Connor-Kelly/ENGI301/docs/GUI_Diagram.png

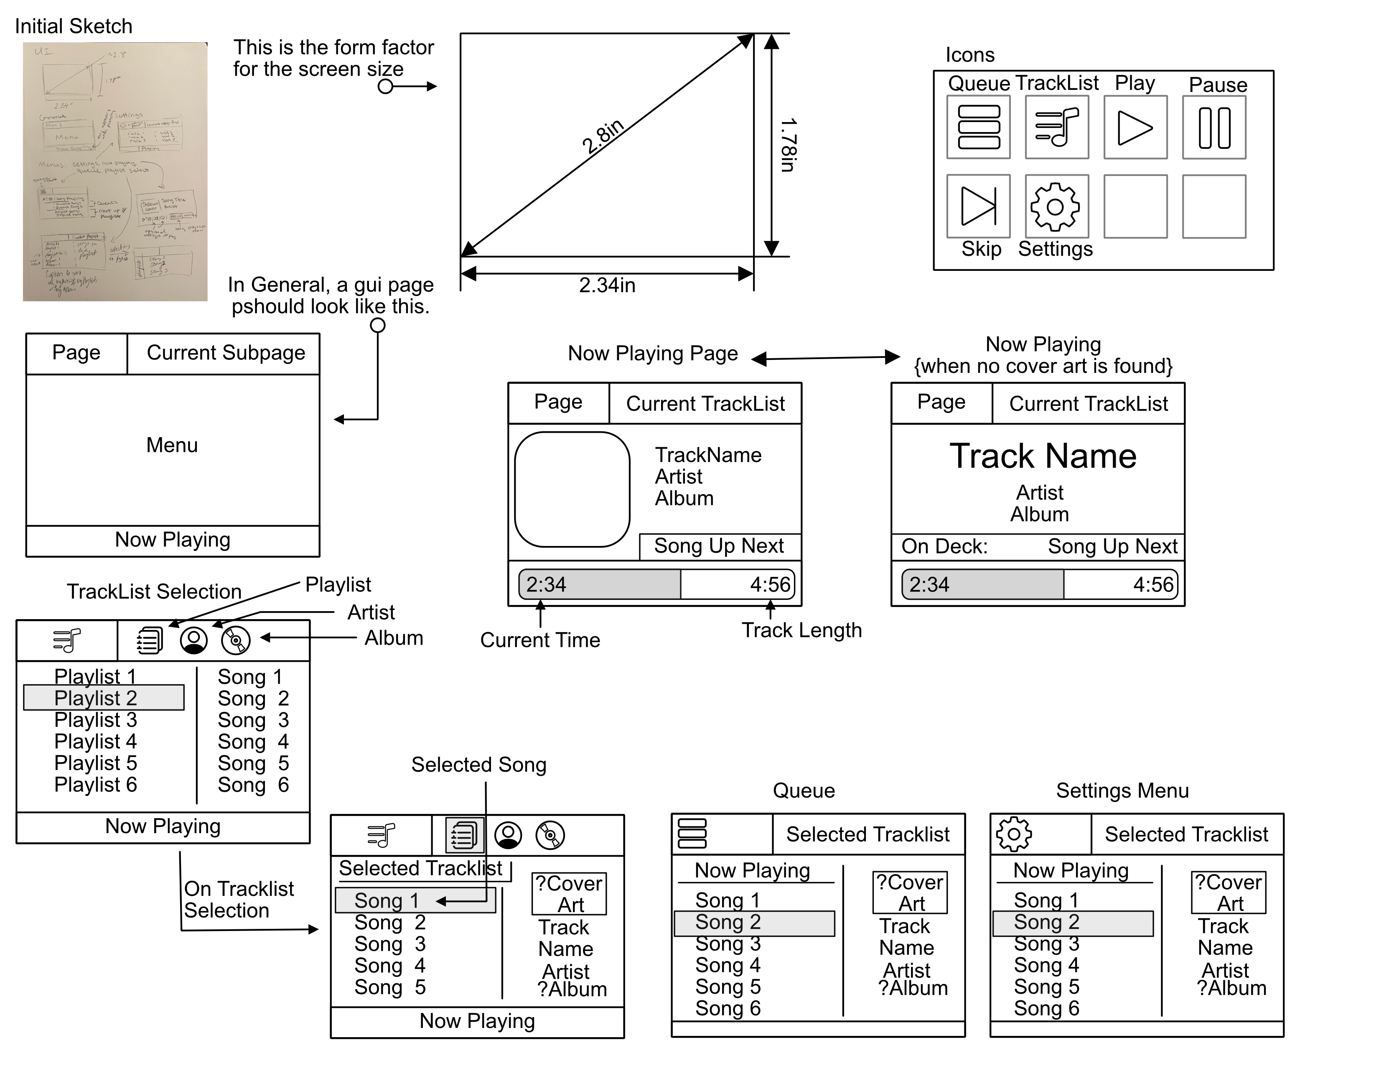
docs/GUI_Diagram.png
