Connor-Kelly/ENGI301/docs/Power_Block_Diagram.png

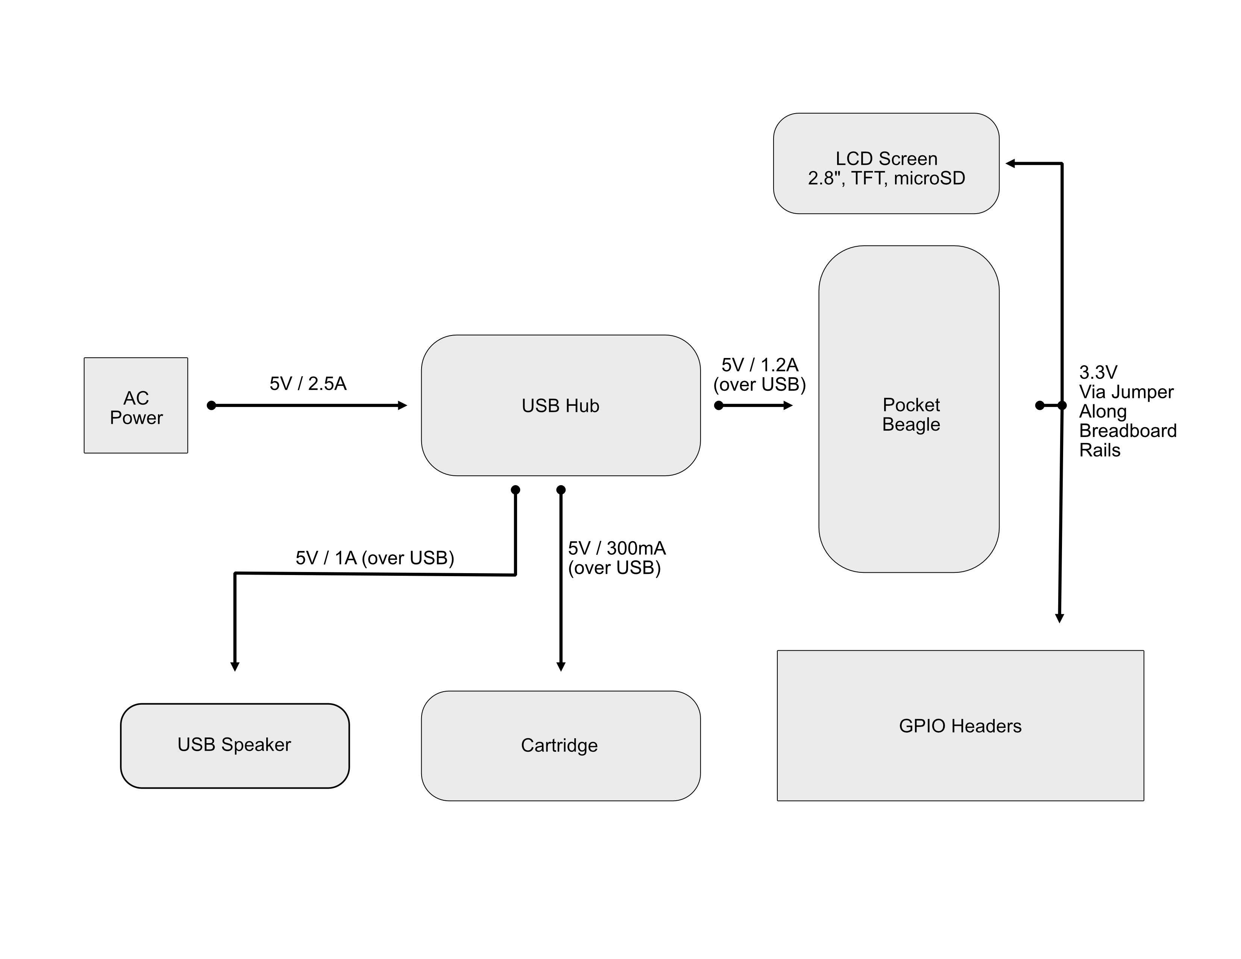
docs/Power_Block_Diagram.png
