Connor-Kelly/ENGI301/docs/Software_Diagram.png

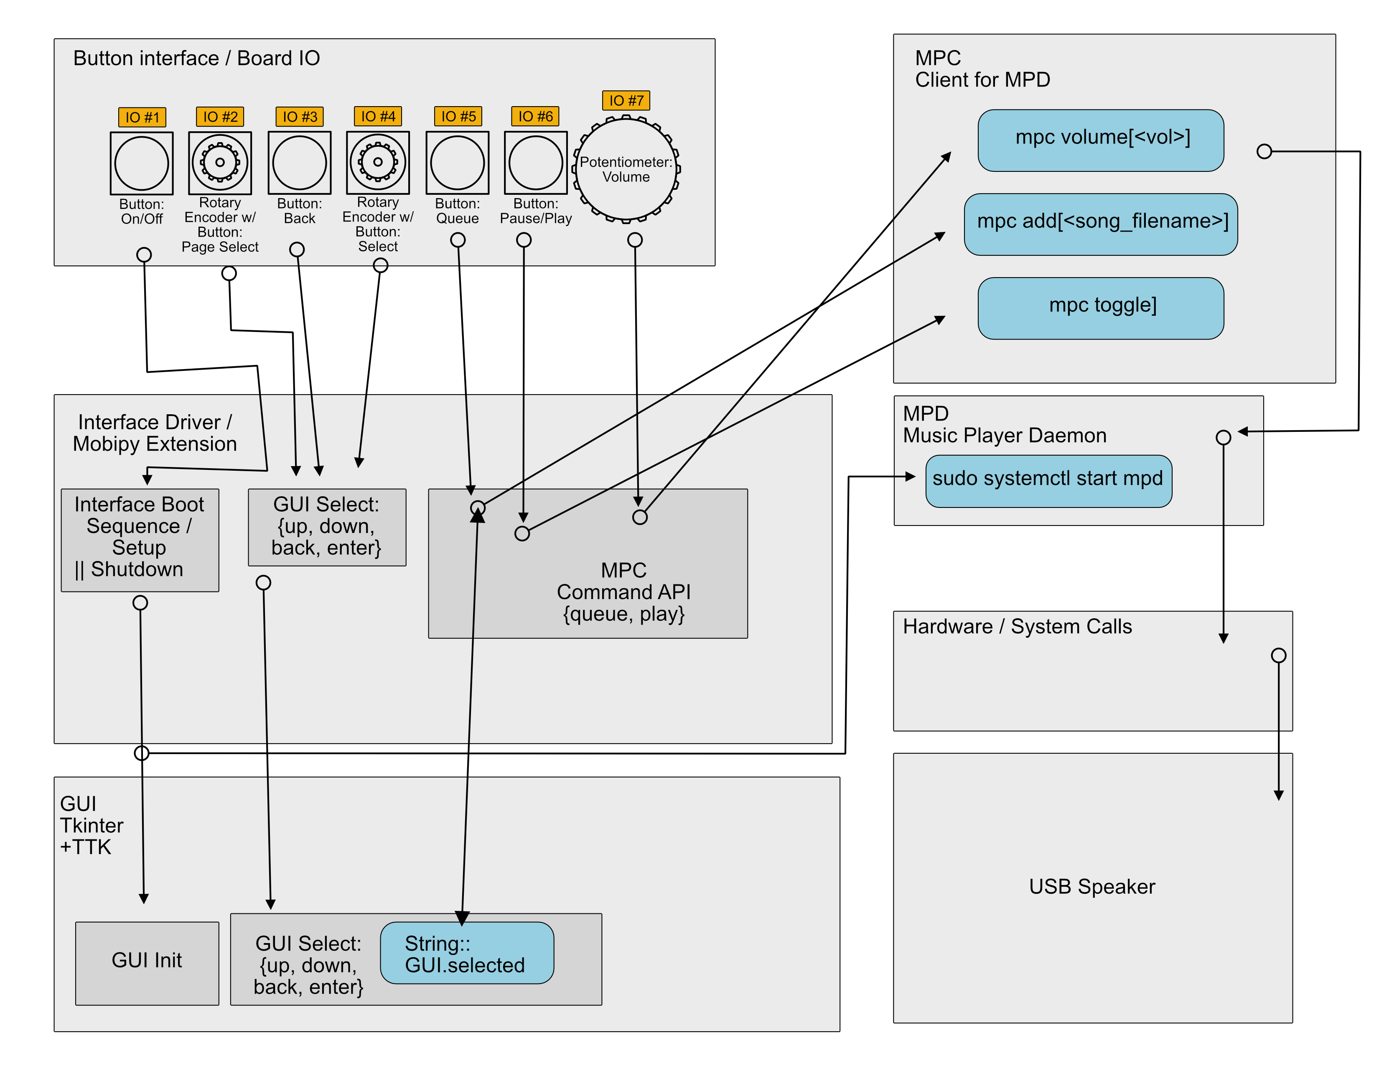
docs/Software_Diagram.png
