Connor-Kelly/ENGI301/docs/System_Block_Diagram.png

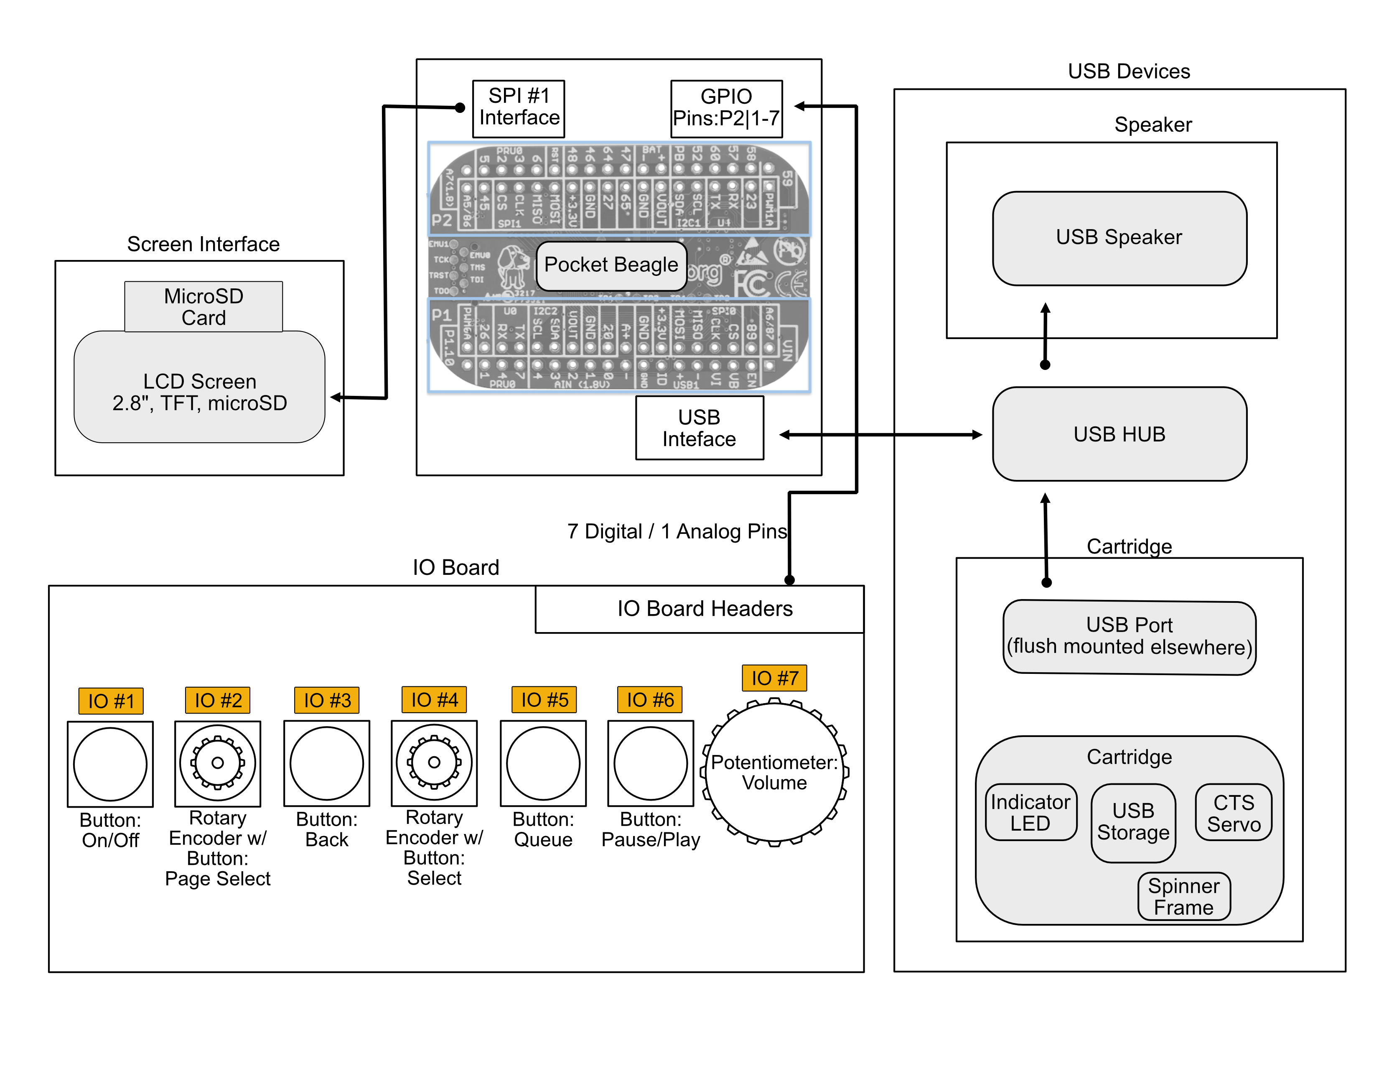
docs/System_Block_Diagram.png
