Connor-Kelly/ENGI301/project_01/images/IMG_2388.jpg

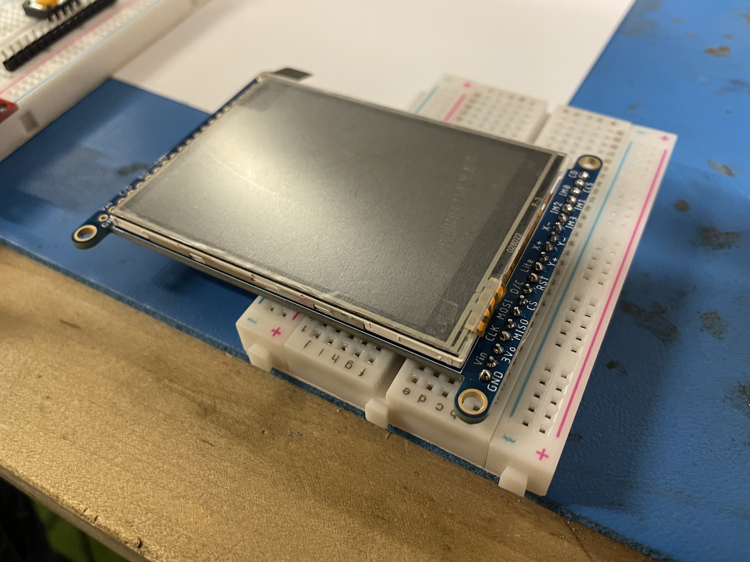
project_01/images/IMG_2388.jpg
