Connor-Kelly/ENGI301/project_01/images/IMG_2392.jpg

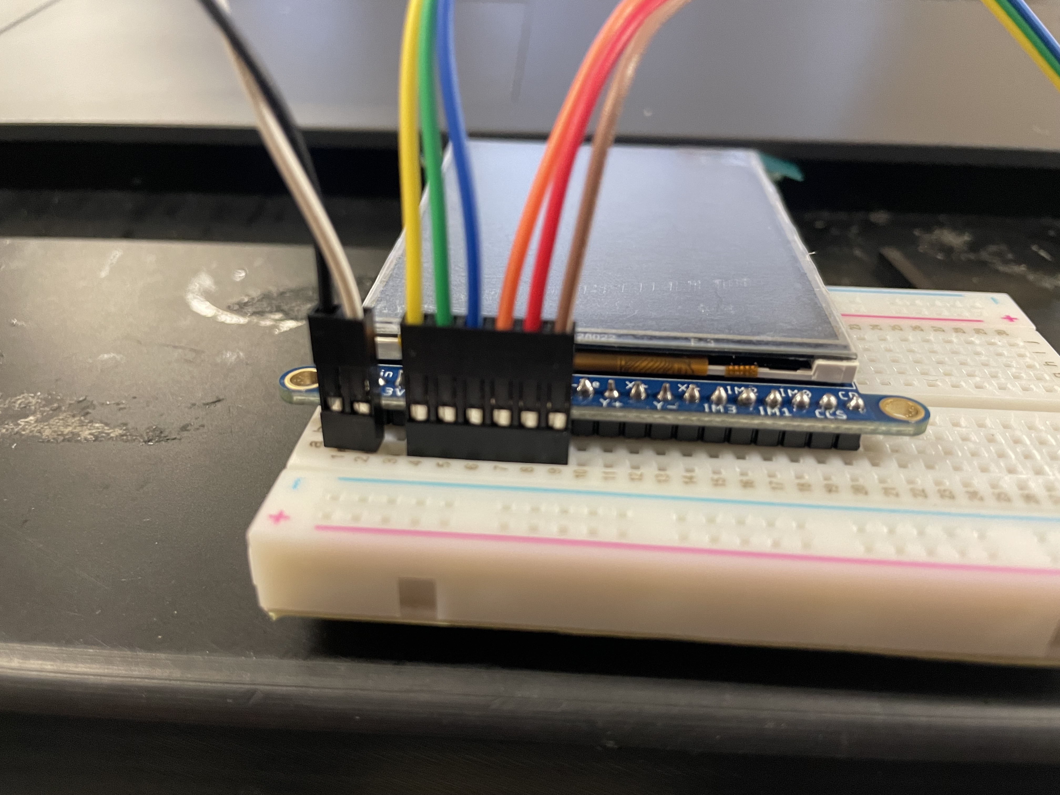
project_01/images/IMG_2392.jpg
