Connor-Kelly/ENGI301/project_01/images/IMG_2395.jpg

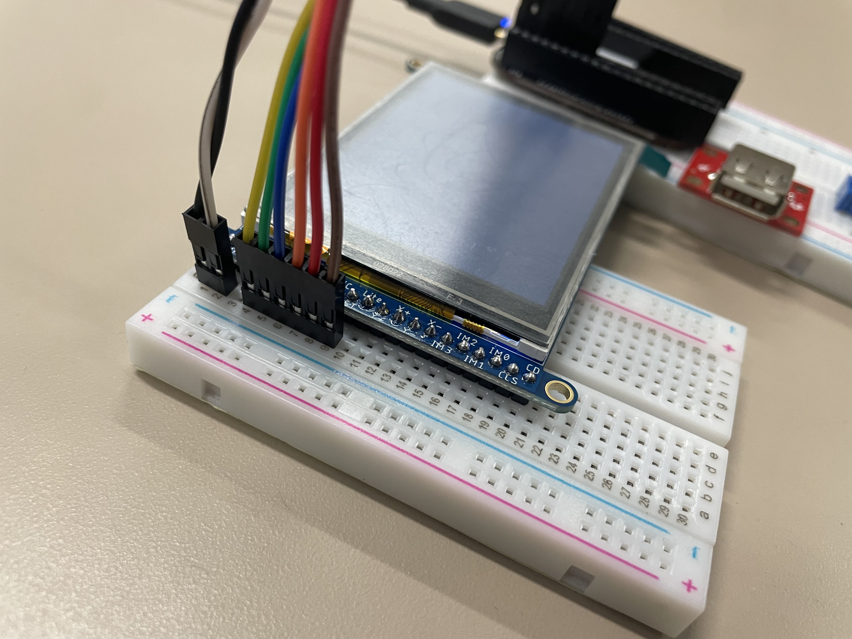
project_01/images/IMG_2395.jpg
