Connor-Kelly/ENGI301/project_01/src/base_gui.png

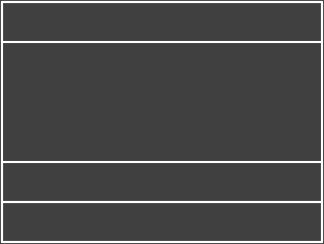
project_01/src/base_gui.png
