Connor-Kelly/ENGI301/docs/GUI_Sketch.jpg

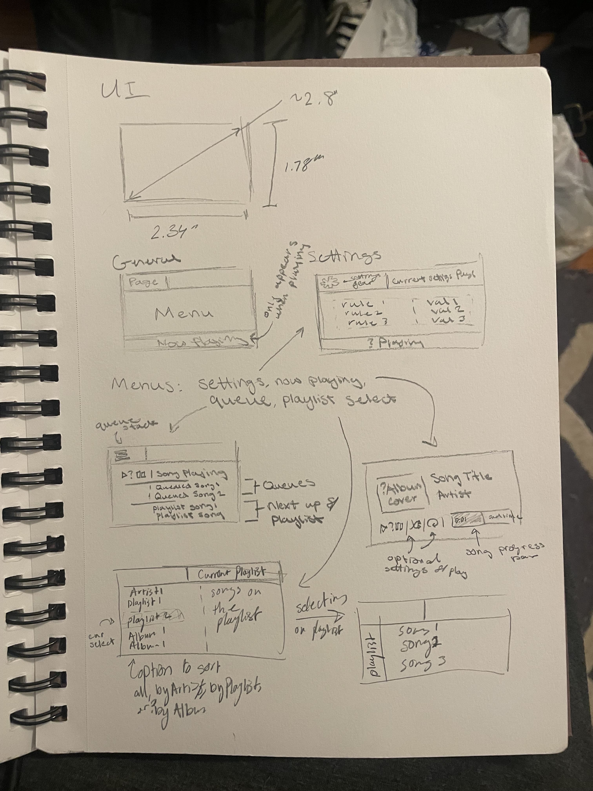
docs/GUI_Sketch.jpg
