Connor-Kelly/ENGI301/project_01/images/IMG_2382.jpg

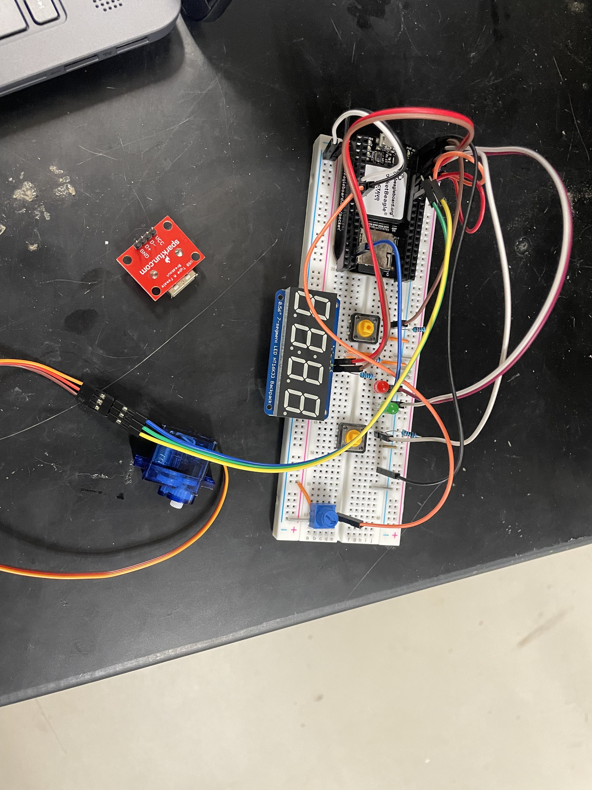
project_01/images/IMG_2382.jpg
