Connor-Kelly/ENGI301/project_01/images/IMG_2384.jpg

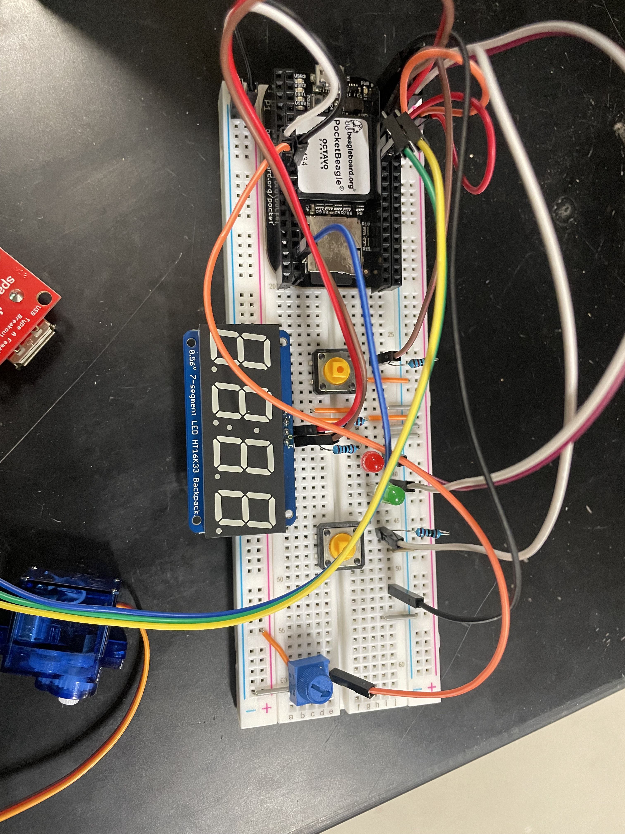
project_01/images/IMG_2384.jpg
