Connor-Kelly/ENGI301/project_01/images/IMG_2401.jpg

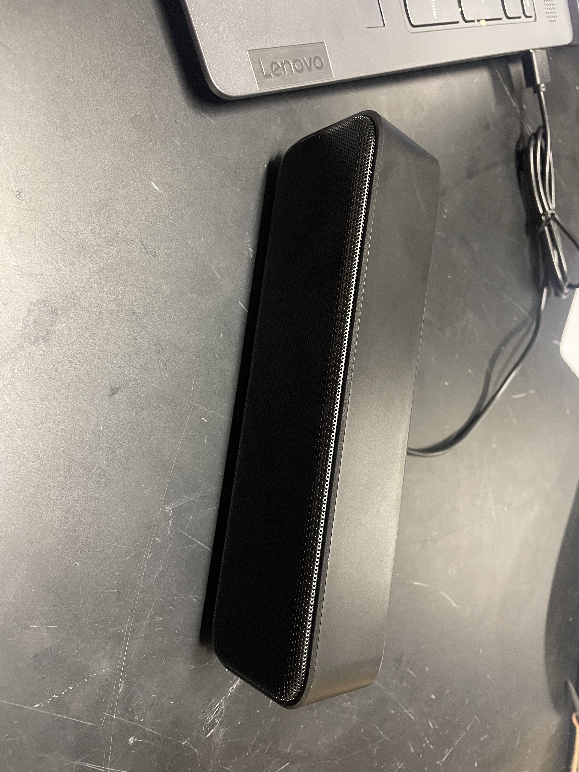
project_01/images/IMG_2401.jpg
