Connor-Kelly/ENGI301/project_01/images/IMG_2410.jpg

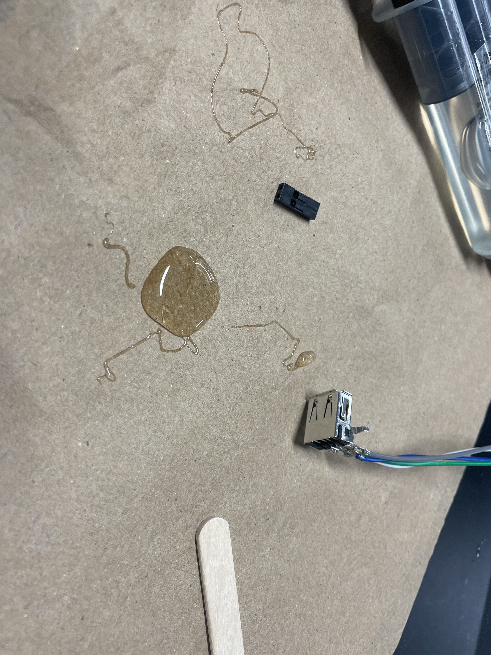
project_01/images/IMG_2410.jpg
