Connor-Kelly/ENGI301/project_01/images/IMG_2411.jpg

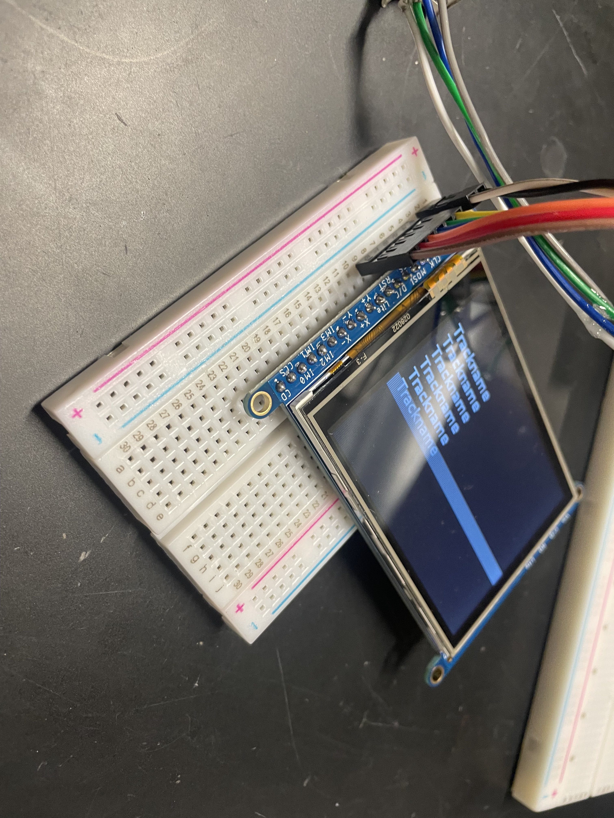
project_01/images/IMG_2411.jpg
