Connor-Kelly/ENGI301/project_01/images/IMG_2413.jpg

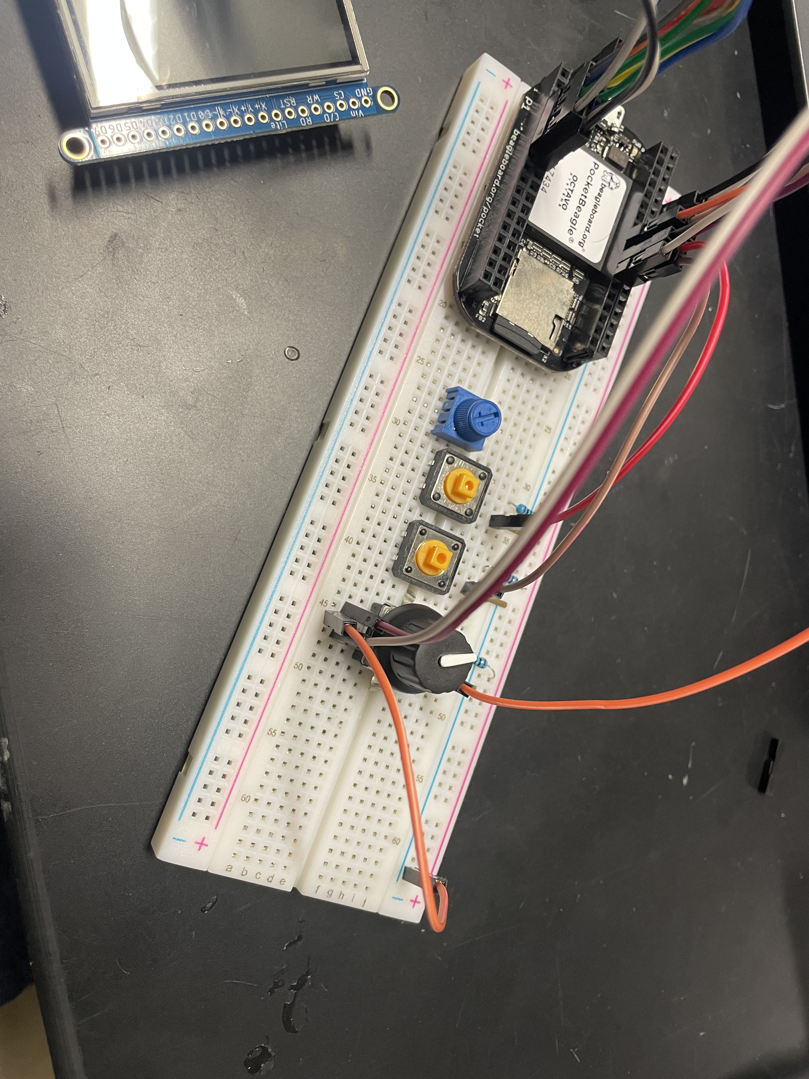
project_01/images/IMG_2413.jpg
